KunYi/study_odrive/analysis/motor_analysis/350kvTP.PNG

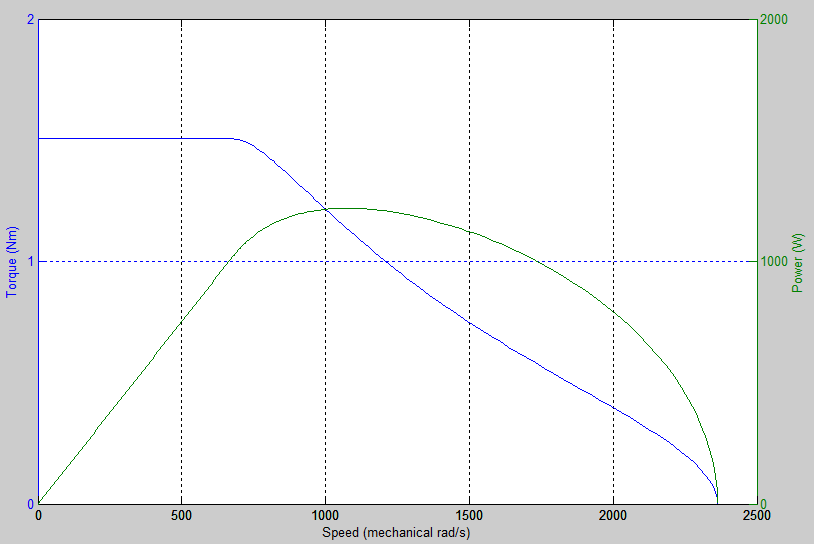
analysis/motor_analysis/350kvTP.PNG
