KunYi/study_odrive/analysis/motor_analysis/350kvVelli.PNG

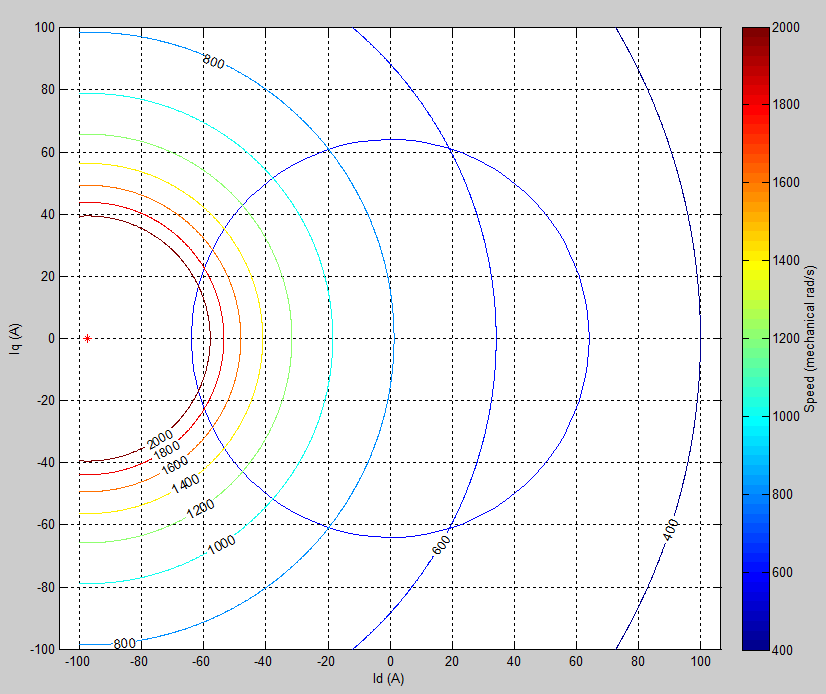
analysis/motor_analysis/350kvVelli.PNG
