KunYi/study_odrive/docs/figures/controller_with_ff.png

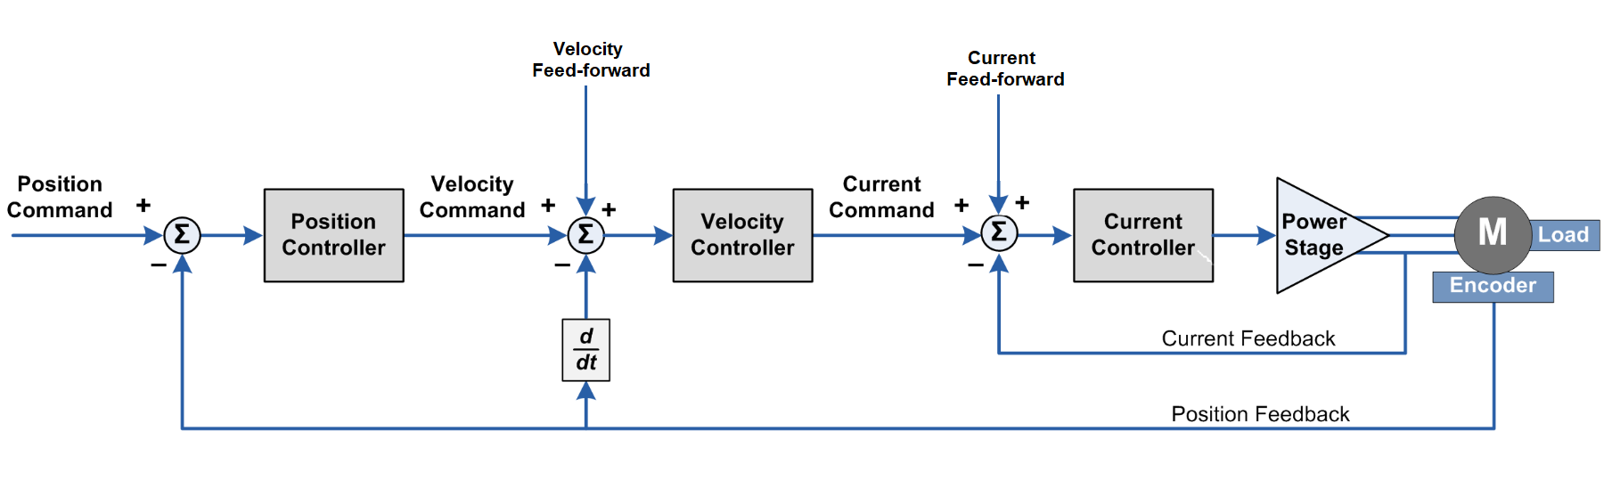
docs/figures/controller_with_ff.png
