KunYi/study_odrive/docs/figures/Endstop_configuration.png

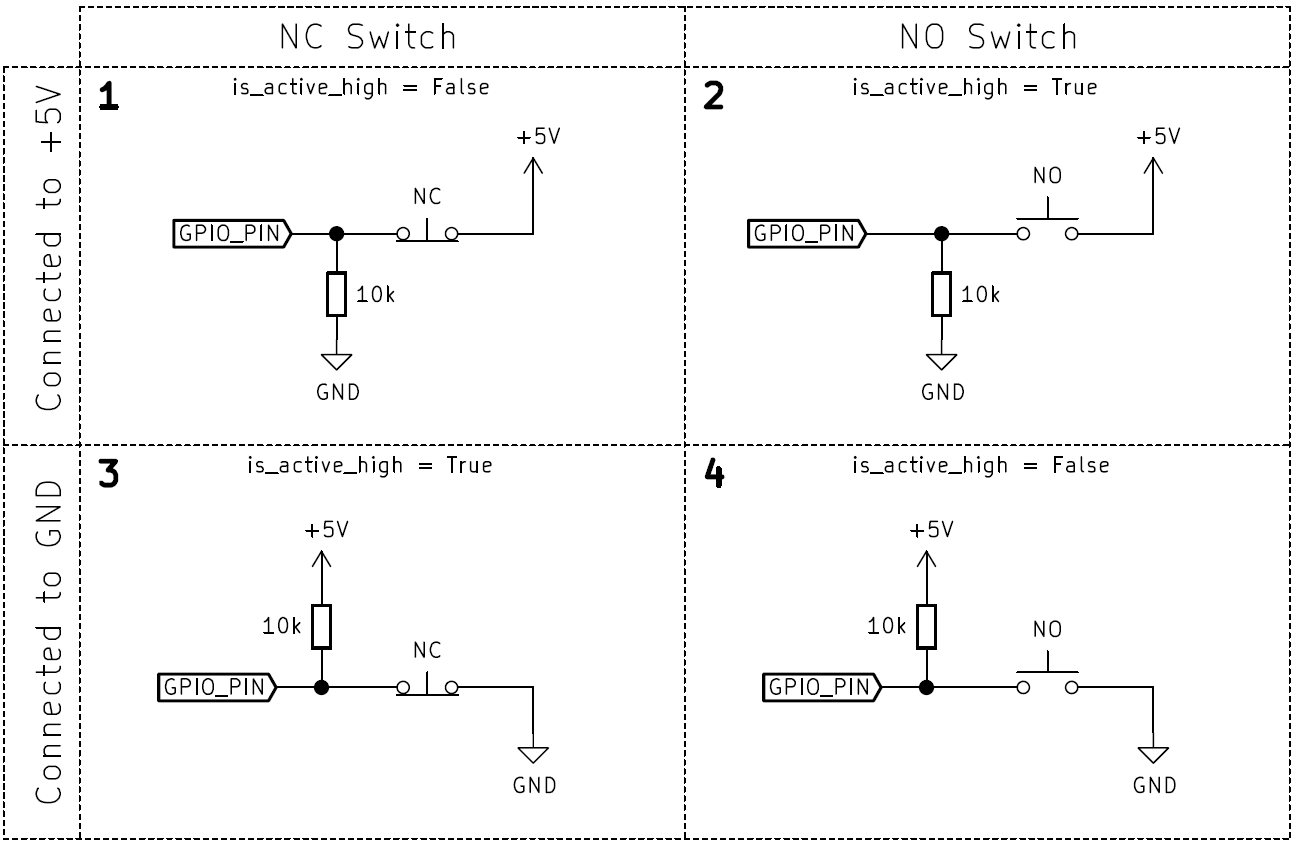
docs/figures/Endstop_configuration.png
