KunYi/study_odrive/docs/figures/ground_loop_bad.png

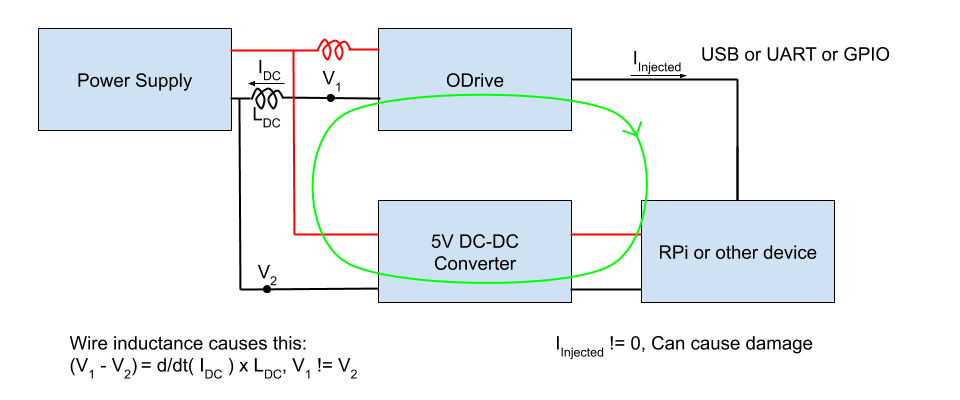
docs/figures/ground_loop_bad.png
