KunYi/study_odrive/docs/figures/ImportLaunch.png

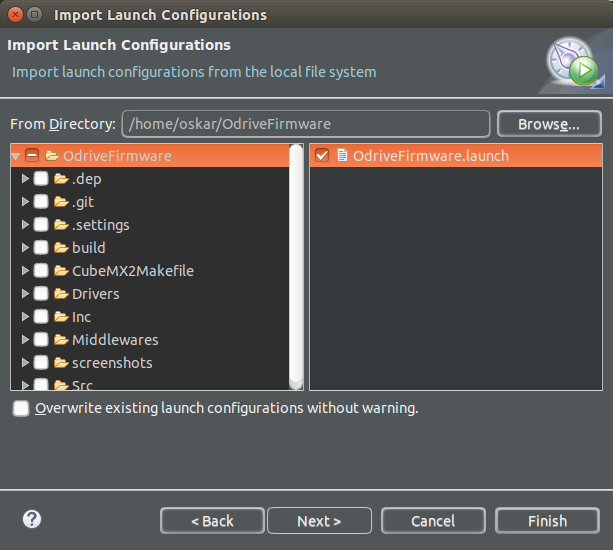
docs/figures/ImportLaunch.png
