KunYi/study_odrive/docs/figures/liveplotter-iq-omega.png

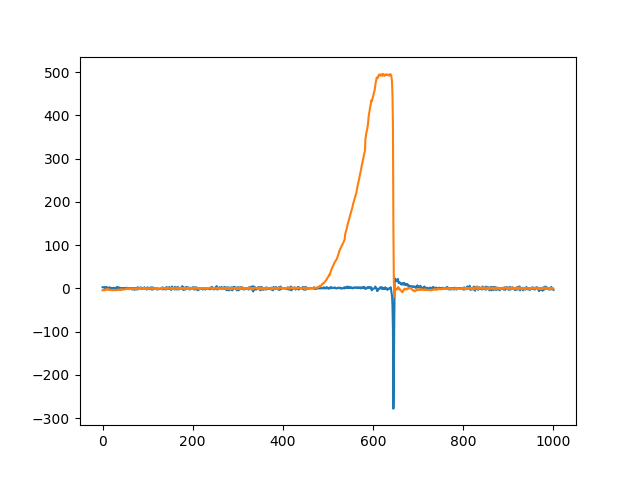
docs/figures/liveplotter-iq-omega.png
