KunYi/study_odrive/docs/figures/mech_dimensions.png

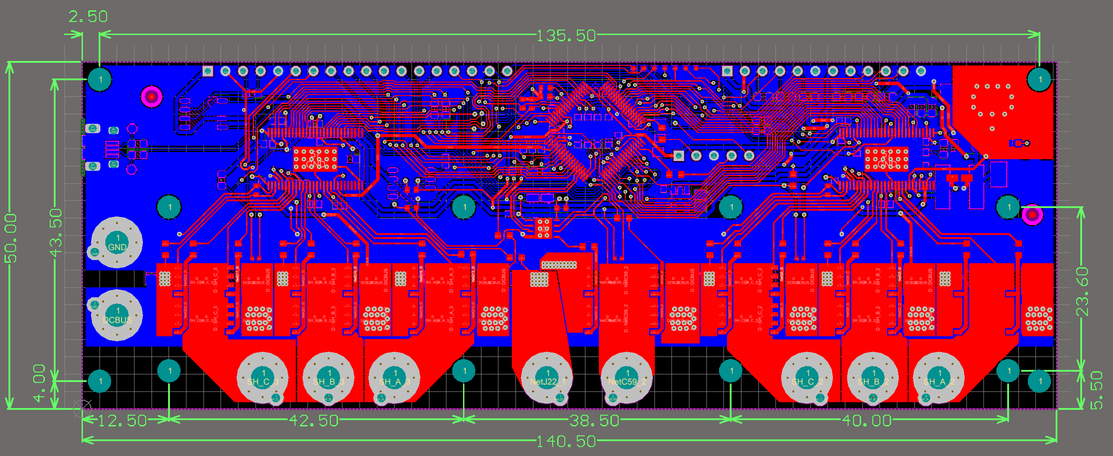
docs/figures/mech_dimensions.png
