KunYi/study_odrive/docs/figures/torque_mode_vel_limit.png

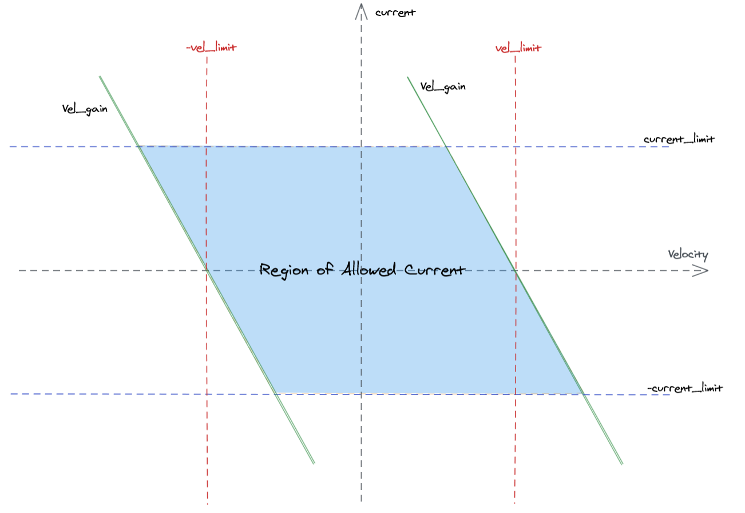
docs/figures/torque_mode_vel_limit.png
