KunYi/study_odrive/docs/figures/TrapTrajPosVel.PNG

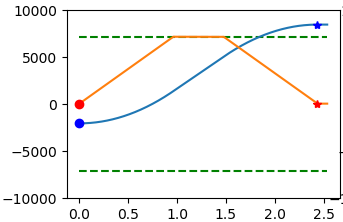
docs/figures/TrapTrajPosVel.PNG
