KunYi/study_odrive/Firmware/motor_timing.jpg

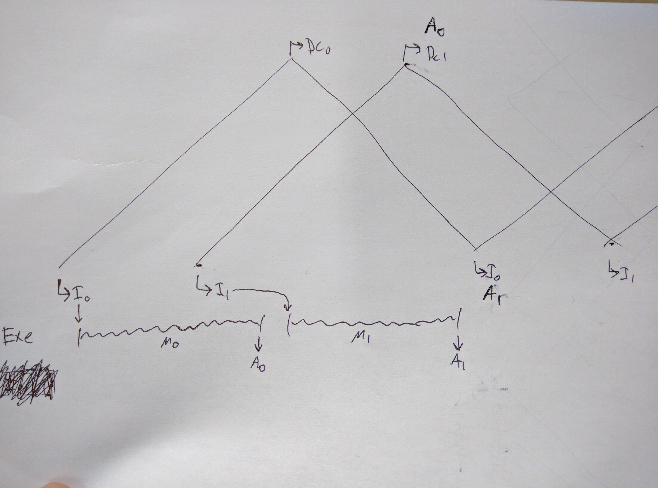
Firmware/motor_timing.jpg
