KunYi/study_odrive/GUI/fibre-js/example.gif

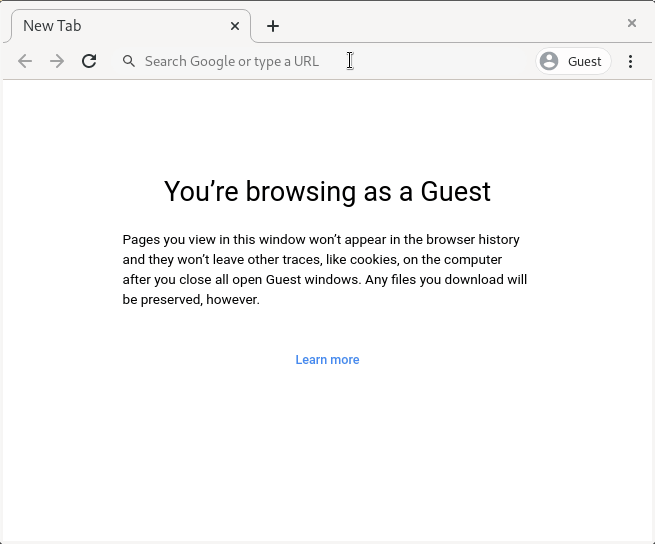
GUI/fibre-js/example.gif
