KunYi/study_odrive/GUI/src/assets/images/24v_300x300.png

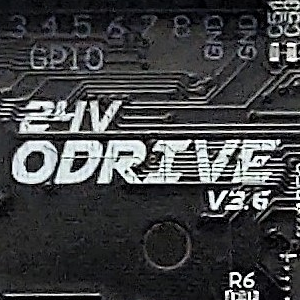
GUI/src/assets/images/24v_300x300.png
