KunYi/study_odrive/GUI/src/assets/images/amt102-v_300x300.png

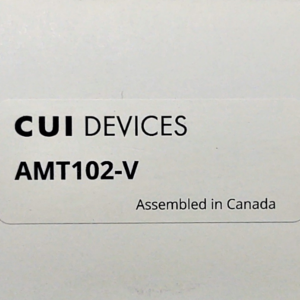
GUI/src/assets/images/amt102-v_300x300.png
