KunYi/study_odrive/GUI/src/assets/images/D5065_300x300.png

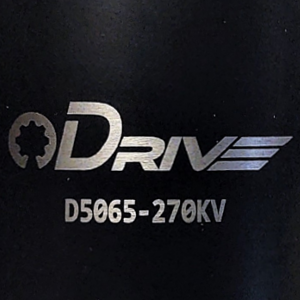
GUI/src/assets/images/D5065_300x300.png
