KunYi/study_odrive/GUI/src/assets/images/D6374_300x300.png

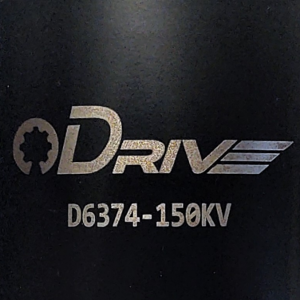
GUI/src/assets/images/D6374_300x300.png
