KunYi/study_odrive/GUI/src/assets/images/M0_300x300.png

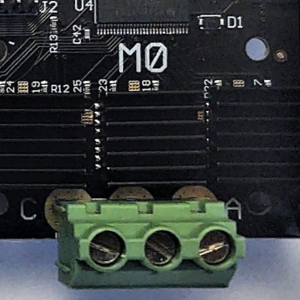
GUI/src/assets/images/M0_300x300.png
