KunYi/study_odrive/GUI/src/assets/images/M0M1_300x300.png

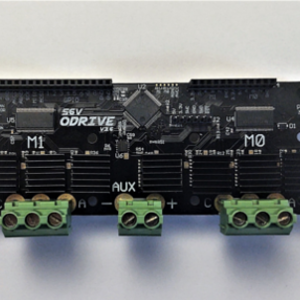
GUI/src/assets/images/M0M1_300x300.png
