KunYi/study_odrive/GUI/src/assets/images/temp.png

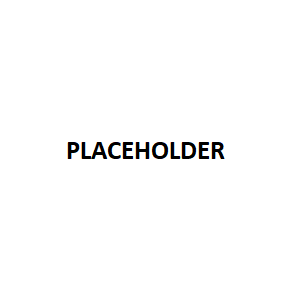
GUI/src/assets/images/temp.png
