KunYi/study_odrive/study/trigonometric.png

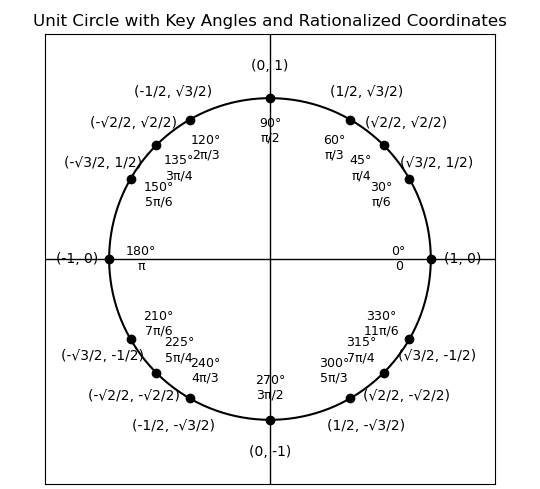
study/trigonometric.png
