KunYi/study_odrive/docs/figures/secondOrderResponse.PNG

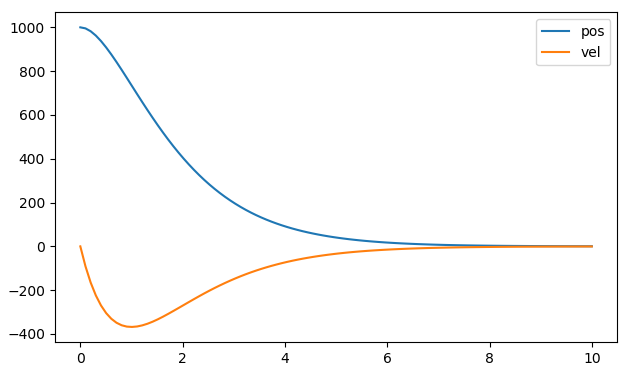
docs/figures/secondOrderResponse.PNG
