KunYi/study_odrive/docs/figures/CodeAsMakefile.png

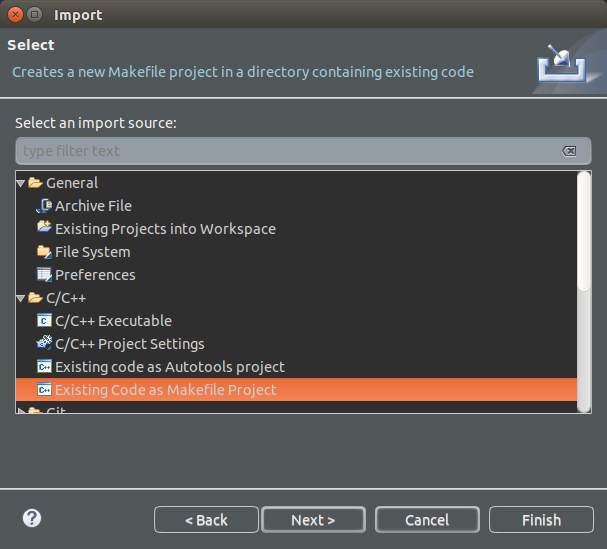
docs/figures/CodeAsMakefile.png
