KunYi/study_odrive/docs/figures/stlink-wiring.jpg

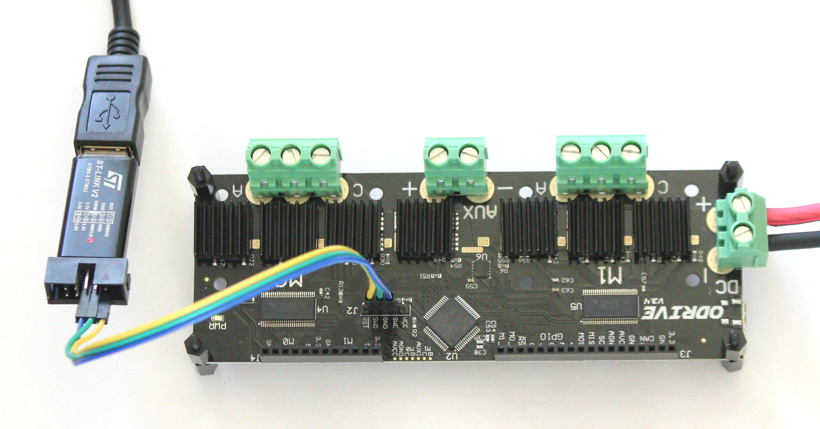
docs/figures/stlink-wiring.jpg
