KunYi/study_odrive/docs/figures/ground_loop_fix.png

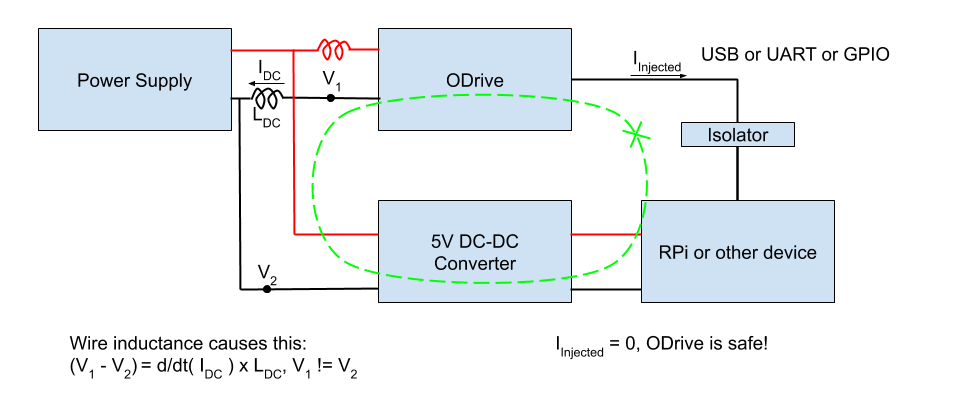
docs/figures/ground_loop_fix.png
