KunYi/study_odrive/Firmware/Board/v3/Src/adc.c

/**
  ******************************************************************************
  * File Name          : ADC.c
  * Description        : This file provides code for the configuration
  *                      of the ADC instances.
  ******************************************************************************
  * This notice applies to any and all portions of this file
  * that are not between comment pairs USER CODE BEGIN and
  * USER CODE END. Other portions of this file, whether 
  * inserted by the user or by software development tools
  * are owned by their respective copyright owners.
  *
  * Copyright (c) 2018 STMicroelectronics International N.V. 
  * All rights reserved.
  *
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
  ******************************************************************************
  */

/* Includes ------------------------------------------------------------------*/
#include "adc.h"

#include "gpio.h"
#include "dma.h"

/* USER CODE BEGIN 0 */

#if HW_VERSION_MAJOR == 3 && HW_VERSION_MINOR == 1 \
||  HW_VERSION_MAJOR == 3 && HW_VERSION_MINOR == 2
#include "prev_board_ver/adc_V3_2.c"
#elif HW_VERSION_MAJOR == 3 && HW_VERSION_MINOR == 3 \
||  HW_VERSION_MAJOR == 3 && HW_VERSION_MINOR == 4
#include "prev_board_ver/adc_V3_4.c"
#else
/* USER CODE END 0 */

ADC_HandleTypeDef hadc1;
ADC_HandleTypeDef hadc2;
ADC_HandleTypeDef hadc3;
DMA_HandleTypeDef hdma_adc1;

/* ADC1 init function */
void MX_ADC1_Init(void)
{
  ADC_ChannelConfTypeDef sConfig;
  ADC_InjectionConfTypeDef sConfigInjected;

    /**Configure the global features of the ADC (Clock, Resolution, Data Alignment and number of conversion) 
    */
  hadc1.Instance = ADC1;
  hadc1.Init.ClockPrescaler = ADC_CLOCK_SYNC_PCLK_DIV4;
  hadc1.Init.Resolution = ADC_RESOLUTION_12B;
  hadc1.Init.ScanConvMode = DISABLE;
  hadc1.Init.ContinuousConvMode = DISABLE;
  hadc1.Init.DiscontinuousConvMode = DISABLE;
  hadc1.Init.ExternalTrigConvEdge = ADC_EXTERNALTRIGCONVEDGE_NONE;
  hadc1.Init.ExternalTrigConv = ADC_SOFTWARE_START;
  hadc1.Init.DataAlign = ADC_DATAALIGN_RIGHT;
  hadc1.Init.NbrOfConversion = 1;
  hadc1.Init.DMAContinuousRequests = DISABLE;
  hadc1.Init.EOCSelection = ADC_EOC_SINGLE_CONV;
  if (HAL_ADC_Init(&hadc1) != HAL_OK)
  {
    _Error_Handler(__FILE__, __LINE__);
  }

    /**Configure for the selected ADC regular channel its corresponding rank in the sequencer and its sample time. 
    */
  sConfig.Channel = ADC_CHANNEL_6;
  sConfig.Rank = 1;
  sConfig.SamplingTime = ADC_SAMPLETIME_3CYCLES;
  if (HAL_ADC_ConfigChannel(&hadc1, &sConfig) != HAL_OK)
  {
    _Error_Handler(__FILE__, __LINE__);
  }

    /**Configures for the selected ADC injected channel its corresponding rank in the sequencer and its sample time 
    */
  sConfigInjected.InjectedChannel = ADC_CHANNEL_6;
  sConfigInjected.InjectedRank = 1;
  sConfigInjected.InjectedNbrOfConversion = 1;
  sConfigInjected.InjectedSamplingTime = ADC_SAMPLETIME_3CYCLES;
  sConfigInjected.ExternalTrigInjecConvEdge = ADC_EXTERNALTRIGINJECCONVEDGE_RISING;
  sConfigInjected.ExternalTrigInjecConv = ADC_EXTERNALTRIGINJECCONV_T1_TRGO;
  sConfigInjected.AutoInjectedConv = DISABLE;
  sConfigInjected.InjectedDiscontinuousConvMode = DISABLE;
  sConfigInjected.InjectedOffset = 0;
  if (HAL_ADCEx_InjectedConfigChannel(&hadc1, &sConfigInjected) != HAL_OK)
  {
    _Error_Handler(__FILE__, __LINE__);
  }

}
/* ADC2 init function */
void MX_ADC2_Init(void)
{
  ADC_ChannelConfTypeDef sConfig;
  ADC_InjectionConfTypeDef sConfigInjected;

    /**Configure the global features of the ADC (Clock, Resolution, Data Alignment and number of conversion) 
    */
  hadc2.Instance = ADC2;
  hadc2.Init.ClockPrescaler = ADC_CLOCK_SYNC_PCLK_DIV4;
  hadc2.Init.Resolution = ADC_RESOLUTION_12B;
  hadc2.Init.ScanConvMode = DISABLE;
  hadc2.Init.ContinuousConvMode = DISABLE;
  hadc2.Init.DiscontinuousConvMode = DISABLE;
  hadc2.Init.ExternalTrigConvEdge = ADC_EXTERNALTRIGCONVEDGE_RISING;
  hadc2.Init.ExternalTrigConv = ADC_EXTERNALTRIGCONV_T8_TRGO;
  hadc2.Init.DataAlign = ADC_DATAALIGN_RIGHT;
  hadc2.Init.NbrOfConversion = 1;
  hadc2.Init.DMAContinuousRequests = DISABLE;
  hadc2.Init.EOCSelection = ADC_EOC_SINGLE_CONV;
  if (HAL_ADC_Init(&hadc2) != HAL_OK)
  {
    _Error_Handler(__FILE__, __LINE__);
  }

    /**Configure for the selected ADC regular channel its corresponding rank in the sequencer and its sample time. 
    */
  sConfig.Channel = ADC_CHANNEL_13;
  sConfig.Rank = 1;
  sConfig.SamplingTime = ADC_SAMPLETIME_3CYCLES;
  if (HAL_ADC_ConfigChannel(&hadc2, &sConfig) != HAL_OK)
  {
    _Error_Handler(__FILE__, __LINE__);
  }

    /**Configures for the selected ADC injected channel its corresponding rank in the sequencer and its sample time 
    */
  sConfigInjected.InjectedChannel = ADC_CHANNEL_10;
  sConfigInjected.InjectedRank = 1;
  sConfigInjected.InjectedNbrOfConversion = 1;
  sConfigInjected.InjectedSamplingTime = ADC_SAMPLETIME_3CYCLES;
  sConfigInjected.ExternalTrigInjecConvEdge = ADC_EXTERNALTRIGINJECCONVEDGE_RISING;
  sConfigInjected.ExternalTrigInjecConv = ADC_EXTERNALTRIGINJECCONV_T1_TRGO;
  sConfigInjected.AutoInjectedConv = DISABLE;
  sConfigInjected.InjectedDiscontinuousConvMode = DISABLE;
  sConfigInjected.InjectedOffset = 0;
  if (HAL_ADCEx_InjectedConfigChannel(&hadc2, &sConfigInjected) != HAL_OK)
  {
    _Error_Handler(__FILE__, __LINE__);
  }

}
/* ADC3 init function */
void MX_ADC3_Init(void)
{
  ADC_ChannelConfTypeDef sConfig;
  ADC_InjectionConfTypeDef sConfigInjected;

    /**Configure the global features of the ADC (Clock, Resolution, Data Alignment and number of conversion) 
    */
  hadc3.Instance = ADC3;
  hadc3.Init.ClockPrescaler = ADC_CLOCK_SYNC_PCLK_DIV4;
  hadc3.Init.Resolution = ADC_RESOLUTION_12B;
  hadc3.Init.ScanConvMode = DISABLE;
  hadc3.Init.ContinuousConvMode = DISABLE;
  hadc3.Init.DiscontinuousConvMode = DISABLE;
  hadc3.Init.ExternalTrigConvEdge = ADC_EXTERNALTRIGCONVEDGE_RISING;
  hadc3.Init.ExternalTrigConv = ADC_EXTERNALTRIGCONV_T8_TRGO;
  hadc3.Init.DataAlign = ADC_DATAALIGN_RIGHT;
  hadc3.Init.NbrOfConversion = 1;
  hadc3.Init.DMAContinuousRequests = DISABLE;
  hadc3.Init.EOCSelection = ADC_EOC_SINGLE_CONV;
  if (HAL_ADC_Init(&hadc3) != HAL_OK)
  {
    _Error_Handler(__FILE__, __LINE__);
  }

    /**Configure for the selected ADC regular channel its corresponding rank in the sequencer and its sample time. 
    */
  sConfig.Channel = ADC_CHANNEL_12;
  sConfig.Rank = 1;
  sConfig.SamplingTime = ADC_SAMPLETIME_3CYCLES;
  if (HAL_ADC_ConfigChannel(&hadc3, &sConfig) != HAL_OK)
  {
    _Error_Handler(__FILE__, __LINE__);
  }

    /**Configures for the selected ADC injected channel its corresponding rank in the sequencer and its sample time 
    */
  sConfigInjected.InjectedChannel = ADC_CHANNEL_11;
  sConfigInjected.InjectedRank = 1;
  sConfigInjected.InjectedNbrOfConversion = 1;
  sConfigInjected.InjectedSamplingTime = ADC_SAMPLETIME_3CYCLES;
  sConfigInjected.ExternalTrigInjecConvEdge = ADC_EXTERNALTRIGINJECCONVEDGE_RISING;
  sConfigInjected.ExternalTrigInjecConv = ADC_EXTERNALTRIGINJECCONV_T1_TRGO;
  sConfigInjected.AutoInjectedConv = DISABLE;
  sConfigInjected.InjectedDiscontinuousConvMode = DISABLE;
  sConfigInjected.InjectedOffset = 0;
  if (HAL_ADCEx_InjectedConfigChannel(&hadc3, &sConfigInjected) != HAL_OK)
  {
    _Error_Handler(__FILE__, __LINE__);
  }

}

void HAL_ADC_MspInit(ADC_HandleTypeDef* adcHandle)
{

  GPIO_InitTypeDef GPIO_InitStruct;
  if(adcHandle->Instance==ADC1)
  {
    /* ADC1 clock enable */
    __HAL_RCC_ADC1_CLK_ENABLE();
  
    /**ADC1 GPIO Configuration    
    PC0     ------> ADC1_IN10
    PC1     ------> ADC1_IN11
    PC2     ------> ADC1_IN12
    PC3     ------> ADC1_IN13
    PA4     ------> ADC1_IN4
    PA5     ------> ADC1_IN5
    PA6     ------> ADC1_IN6
    PC5     ------> ADC1_IN15 
    */
    GPIO_InitStruct.Pin = M0_IB_Pin|M0_IC_Pin|M1_IC_Pin|M1_IB_Pin 
                          |M0_TEMP_Pin;
    GPIO_InitStruct.Mode = GPIO_MODE_ANALOG;
    GPIO_InitStruct.Pull = GPIO_NOPULL;
    HAL_GPIO_Init(GPIOC, &GPIO_InitStruct);

    GPIO_InitStruct.Pin = M1_TEMP_Pin|AUX_TEMP_Pin|VBUS_S_Pin;
    GPIO_InitStruct.Mode = GPIO_MODE_ANALOG;
    GPIO_InitStruct.Pull = GPIO_NOPULL;
    HAL_GPIO_Init(GPIOA, &GPIO_InitStruct);

    /* ADC1 DMA Init */
    /* ADC1 Init */
    hdma_adc1.Instance = DMA2_Stream0;
    hdma_adc1.Init.Channel = DMA_CHANNEL_0;
    hdma_adc1.Init.Direction = DMA_PERIPH_TO_MEMORY;
    hdma_adc1.Init.PeriphInc = DMA_PINC_DISABLE;
    hdma_adc1.Init.MemInc = DMA_MINC_ENABLE;
    hdma_adc1.Init.PeriphDataAlignment = DMA_PDATAALIGN_HALFWORD;
    hdma_adc1.Init.MemDataAlignment = DMA_MDATAALIGN_HALFWORD;
    hdma_adc1.Init.Mode = DMA_CIRCULAR;
    hdma_adc1.Init.Priority = DMA_PRIORITY_LOW;
    hdma_adc1.Init.FIFOMode = DMA_FIFOMODE_DISABLE;
    if (HAL_DMA_Init(&hdma_adc1) != HAL_OK)
    {
      _Error_Handler(__FILE__, __LINE__);
    }

    __HAL_LINKDMA(adcHandle,DMA_Handle,hdma_adc1);

  }
  else if(adcHandle->Instance==ADC2)
  {
    /* ADC2 clock enable */
    __HAL_RCC_ADC2_CLK_ENABLE();
  
    /**ADC2 GPIO Configuration    
    PC0     ------> ADC2_IN10
    PC1     ------> ADC2_IN11
    PC2     ------> ADC2_IN12
    PC3     ------> ADC2_IN13
    PA4     ------> ADC2_IN4
    PA5     ------> ADC2_IN5
    PA6     ------> ADC2_IN6
    PC5     ------> ADC2_IN15 
    */
    GPIO_InitStruct.Pin = M0_IB_Pin|M0_IC_Pin|M1_IC_Pin|M1_IB_Pin 
                          |M0_TEMP_Pin;
    GPIO_InitStruct.Mode = GPIO_MODE_ANALOG;
    GPIO_InitStruct.Pull = GPIO_NOPULL;
    HAL_GPIO_Init(GPIOC, &GPIO_InitStruct);

    GPIO_InitStruct.Pin = M1_TEMP_Pin|AUX_TEMP_Pin|VBUS_S_Pin;
    GPIO_InitStruct.Mode = GPIO_MODE_ANALOG;
    GPIO_InitStruct.Pull = GPIO_NOPULL;
    HAL_GPIO_Init(GPIOA, &GPIO_InitStruct);

  }
  else if(adcHandle->Instance==ADC3)
  {
    /* ADC3 clock enable */
    __HAL_RCC_ADC3_CLK_ENABLE();
  
    /**ADC3 GPIO Configuration    
    PC0     ------> ADC3_IN10
    PC1     ------> ADC3_IN11
    PC2     ------> ADC3_IN12
    PC3     ------> ADC3_IN13 
    */
    GPIO_InitStruct.Pin = M0_IB_Pin|M0_IC_Pin|M1_IC_Pin|M1_IB_Pin;
    GPIO_InitStruct.Mode = GPIO_MODE_ANALOG;
    GPIO_InitStruct.Pull = GPIO_NOPULL;
    HAL_GPIO_Init(GPIOC, &GPIO_InitStruct);

  }
}

void HAL_ADC_MspDeInit(ADC_HandleTypeDef* adcHandle)
{

  if(adcHandle->Instance==ADC1)
  {
    /* Peripheral clock disable */
    __HAL_RCC_ADC1_CLK_DISABLE();
  
    /**ADC1 GPIO Configuration    
    PC0     ------> ADC1_IN10
    PC1     ------> ADC1_IN11
    PC2     ------> ADC1_IN12
    PC3     ------> ADC1_IN13
    PA4     ------> ADC1_IN4
    PA5     ------> ADC1_IN5
    PA6     ------> ADC1_IN6
    PC5     ------> ADC1_IN15 
    */
    HAL_GPIO_DeInit(GPIOC, M0_IB_Pin|M0_IC_Pin|M1_IC_Pin|M1_IB_Pin 
                          |M0_TEMP_Pin);

    HAL_GPIO_DeInit(GPIOA, M1_TEMP_Pin|AUX_TEMP_Pin|VBUS_S_Pin);

    /* ADC1 DMA DeInit */
    HAL_DMA_DeInit(adcHandle->DMA_Handle);

    /* ADC1 interrupt Deinit */
  /* USER CODE BEGIN ADC1:ADC_IRQn disable */
    /**
    * Uncomment the line below to disable the "ADC_IRQn" interrupt
    * Be aware, disabling shared interrupt may affect other IPs
    */
    /* HAL_NVIC_DisableIRQ(ADC_IRQn); */
  /* USER CODE END ADC1:ADC_IRQn disable */

  }
  else if(adcHandle->Instance==ADC2)
  {
    /* Peripheral clock disable */
    __HAL_RCC_ADC2_CLK_DISABLE();
  
    /**ADC2 GPIO Configuration    
    PC0     ------> ADC2_IN10
    PC1     ------> ADC2_IN11
    PC2     ------> ADC2_IN12
    PC3     ------> ADC2_IN13
    PA4     ------> ADC2_IN4
    PA5     ------> ADC2_IN5
    PA6     ------> ADC2_IN6
    PC5     ------> ADC2_IN15 
    */
    HAL_GPIO_DeInit(GPIOC, M0_IB_Pin|M0_IC_Pin|M1_IC_Pin|M1_IB_Pin 
                          |M0_TEMP_Pin);

    HAL_GPIO_DeInit(GPIOA, M1_TEMP_Pin|AUX_TEMP_Pin|VBUS_S_Pin);

    /* ADC2 interrupt Deinit */
  /* USER CODE BEGIN ADC2:ADC_IRQn disable */
    /**
    * Uncomment the line below to disable the "ADC_IRQn" interrupt
    * Be aware, disabling shared interrupt may affect other IPs
    */
    /* HAL_NVIC_DisableIRQ(ADC_IRQn); */
  /* USER CODE END ADC2:ADC_IRQn disable */

  }
  else if(adcHandle->Instance==ADC3)
  {
    /* Peripheral clock disable */
    __HAL_RCC_ADC3_CLK_DISABLE();
  
    /**ADC3 GPIO Configuration    
    PC0     ------> ADC3_IN10
    PC1     ------> ADC3_IN11
    PC2     ------> ADC3_IN12
    PC3     ------> ADC3_IN13 
    */
    HAL_GPIO_DeInit(GPIOC, M0_IB_Pin|M0_IC_Pin|M1_IC_Pin|M1_IB_Pin);

    /* ADC3 interrupt Deinit */
  /* USER CODE BEGIN ADC3:ADC_IRQn disable */
    /**
    * Uncomment the line below to disable the "ADC_IRQn" interrupt
    * Be aware, disabling shared interrupt may affect other IPs
    */
    /* HAL_NVIC_DisableIRQ(ADC_IRQn); */
  /* USER CODE END ADC3:ADC_IRQn disable */

  }
} 

/* USER CODE BEGIN 1 */
#endif  // END ADC Include

/* USER CODE END 1 */

/**
  * @}
  */

/**
  * @}
  */

/************************ (C) COPYRIGHT STMicroelectronics *****END OF FILE****/
