KunYi/study_odrive/analysis/filterpoles.py

import numpy as np
import sympy as sp
from scipy.integrate import solve_ivp
import matplotlib.pyplot as plt

do_mass_spring = True
do_PLL = False

bandwidth = 10

pos_ref = 0
vel_ref = 0
init_pos = 1000
init_vel = 0

plotend = 1
plotfrequency = 1000.0

fig, ax1 = plt.subplots()

if do_mass_spring:
    # 2nd order system response with manipulation of velocity only
    # This is similar to a mass/spring/damper system
    # pos_dot = vel
    # vel_dot = Kp * delta_pos + Ki * delta_vel

    Ki = 2.0 * bandwidth
    Kp = 0.25 * Ki**2

    def get_Xdot(t, X):
        pos = X[0]
        vel = X[1]

        pos_err = pos_ref - pos
        vel_err = vel_ref - vel
        
        pos_dot = vel
        vel_dot = Kp * pos_err + Ki * vel_err

        Xdot = [pos_dot, vel_dot]
        return Xdot

    sol = solve_ivp(get_Xdot, (0.0, plotend), [init_pos, init_vel], t_eval=np.linspace(0, plotend, plotend*plotfrequency))

    color = 'tab:red'
    ax1.set_xlabel('time (s)')
    ax1.set_ylabel('pos', color=color)
    ax1.plot(np.transpose(sol.t), np.transpose(sol.y[0,:]), label='physical mass', color=color)
    ax1.tick_params(axis='y', labelcolor=color)

    ax2 = ax1.twinx()  # instantiate a second axes that shares the same x-axis

    color = 'tab:blue'
    ax2.set_ylabel('vel', color=color)  # we already handled the x-label with ax1
    ax2.plot(np.transpose(sol.t), np.transpose(sol.y[1,:]), label='physical mass', color=color)
    ax2.tick_params(axis='y', labelcolor=color)


if do_PLL:
    # 2nd order system response with a "slipping displacement" term directly on position
    # This formulation is given in the sensorless PLL paper
    # pos_dot = vel + Kp * delta_pos
    # vel_dot = Ki * delta_pos

    Kp = 2.0 * bandwidth
    Ki = 0.25 * Kp**2

    def get_Xdot(t, X):
        pos = X[0]
        vel = X[1]

        pos_err = pos_ref - pos
        vel_err = vel_ref - vel

        pos_dot = vel + Kp * pos_err
        vel_dot = Ki * pos_err

        Xdot = [pos_dot, vel_dot]
        return Xdot

    sol = solve_ivp(get_Xdot, (0.0, plotend), [init_pos, init_vel], t_eval=np.linspace(0, plotend, plotend*plotfrequency))

    plt.plot(np.transpose(sol.t), np.transpose(sol.y[0,:]), label='PLL pos')
    plt.plot(np.transpose(sol.t), np.transpose(sol.y[1,:]), label='PLL vel')



plt.legend()
plt.show(block=True)
