KunYi/study_odrive/tools/odrive/tests/integration_test.py

# this test runs the motor using CAN
# TODO - run a motor using all common use cases (uart, step/dir, pwm)

import test_runner

import struct
import can
import asyncio
import time
import math

from fibre.utils import Logger
from odrive.enums import *
from test_runner import *

# Each argument is described as tuple (name, format, scale).
# Struct format codes: https://docs.python.org/2/library/struct.html
command_set = {
    'heartbeat': (0x001, [('error', 'I', 1), ('current_state', 'I', 1)]), # tested
    'estop': (0x002, []), # tested
    'get_motor_error': (0x003, [('motor_error', 'I', 1)]), # untested
    'get_encoder_error': (0x004, [('encoder_error', 'I', 1)]), # untested
    'get_sensorless_error': (0x005, [('sensorless_error', 'I', 1)]), # untested
    'set_node_id': (0x006, [('node_id', 'I', 1)]), # tested
    'set_requested_state': (0x007, [('requested_state', 'I', 1)]), # tested
    # 0x008 not yet implemented
    'get_encoder_estimates': (0x009, [('encoder_pos_estimate', 'f', 1), ('encoder_vel_estimate', 'f', 1)]), # partially tested
    'get_encoder_count': (0x00a, [('encoder_shadow_count', 'i', 1), ('encoder_count', 'i', 1)]), # partially tested
    'set_controller_modes': (0x00b, [('control_mode', 'i', 1), ('input_mode', 'i', 1)]), # tested
    'set_input_pos': (0x00c, [('input_pos', 'f', 1), ('vel_ff', 'h', 0.001), ('torque_ff', 'h', 0.001)]), # tested
    'set_input_vel': (0x00d, [('input_vel', 'f', 1), ('torque_ff', 'f', 1)]), # tested
    'set_input_torque': (0x00e, [('input_torque', 'f', 1)]), # tested
    'set_velocity_limit': (0x00f, [('velocity_limit', 'f', 1)]), # tested
    'start_anticogging': (0x010, []), # untested
    'set_traj_vel_limit': (0x011, [('traj_vel_limit', 'f', 1)]), # tested
    'set_traj_accel_limits': (0x012, [('traj_accel_limit', 'f', 1), ('traj_decel_limit', 'f', 1)]), # tested
    'set_traj_inertia': (0x013, [('inertia', 'f', 1)]), # tested
    'get_iq': (0x014, [('iq_setpoint', 'f', 1), ('iq_measured', 'f', 1)]), # untested
    'get_sensorless_estimates': (0x015, [('sensorless_pos_estimate', 'f', 1), ('sensorless_vel_estimate', 'f', 1)]), # untested
    'reboot': (0x016, []), # tested
    'get_vbus_voltage': (0x017, [('vbus_voltage', 'f', 1)]), # tested
    'clear_errors': (0x018, []), # partially tested
}
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
